odtu/PCBDesignWClaude/docs/target_preview.png

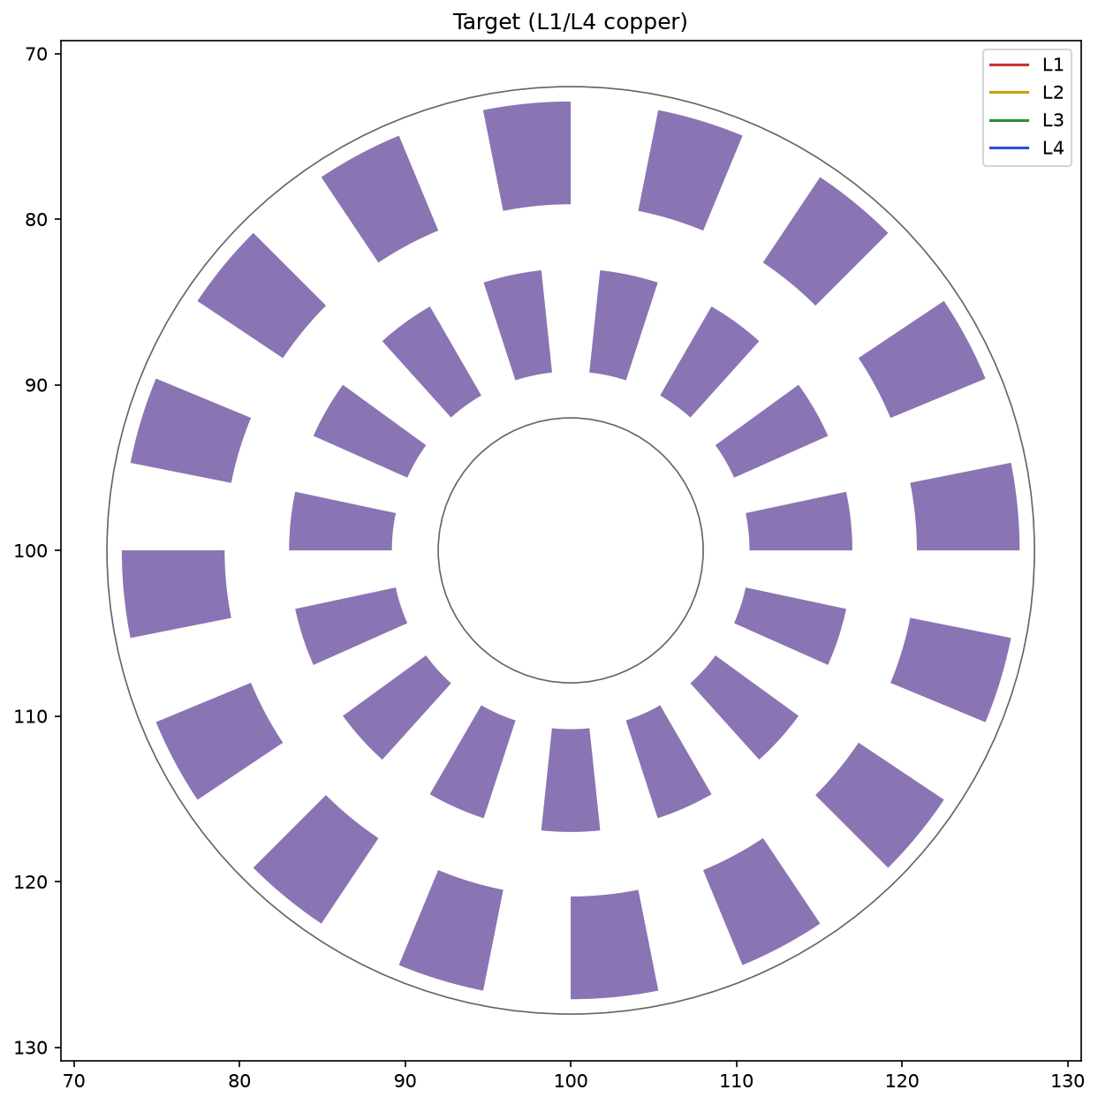
docs/target_preview.png
