odtu/PCBDesignWClaude/docs/views/50-signal-B.png

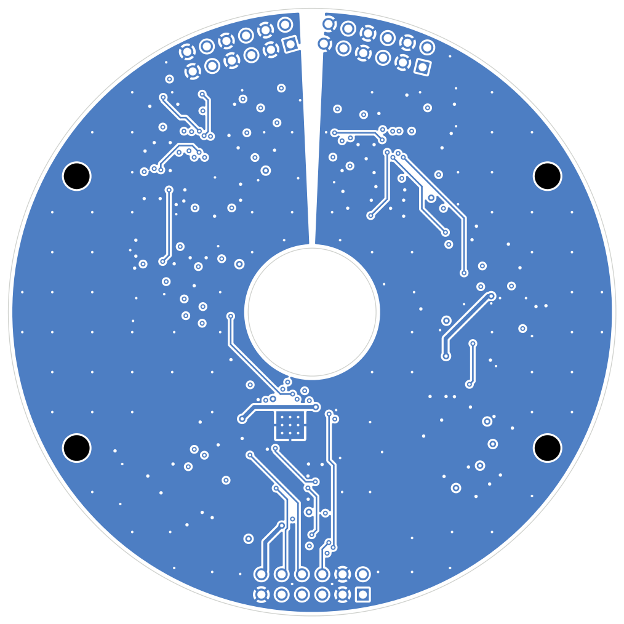
docs/views/50-signal-B.png
